AMagill/GPSClock/display.hpp

#pragma once
#include "time.hpp"
#include <cstdint>
#include <array>
#include <string_view>
#include "hardware/pio.h"

void disp_init(PIO pio, uint tx_pin, uint clk_pin, uint latch_pin);
void disp_latch();
void disp_send(bool latch);
void disp_set_brightness(uint8_t bright);
void disp_clear();
void disp_set_num(uint digit, uint8_t value, bool dp);
void disp_set_raw(uint chip, uint8_t value);
void disp_set_colons(bool on);
void disp_test();
